HunterWhyte/WirelessLEDBracelet/media/case_render.png

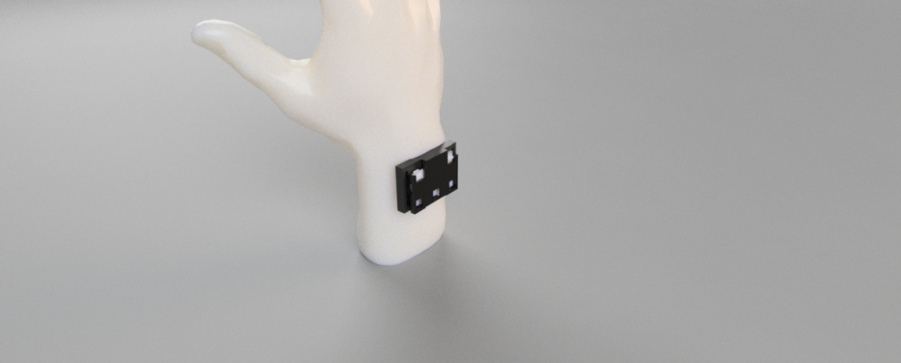
media/case_render.png
