HunterWhyte/WirelessLEDBracelet/bracelet_hardware/bracelet.sch

## EAGLE design bracelet_hardware/bracelet.sch (2023-08-14)

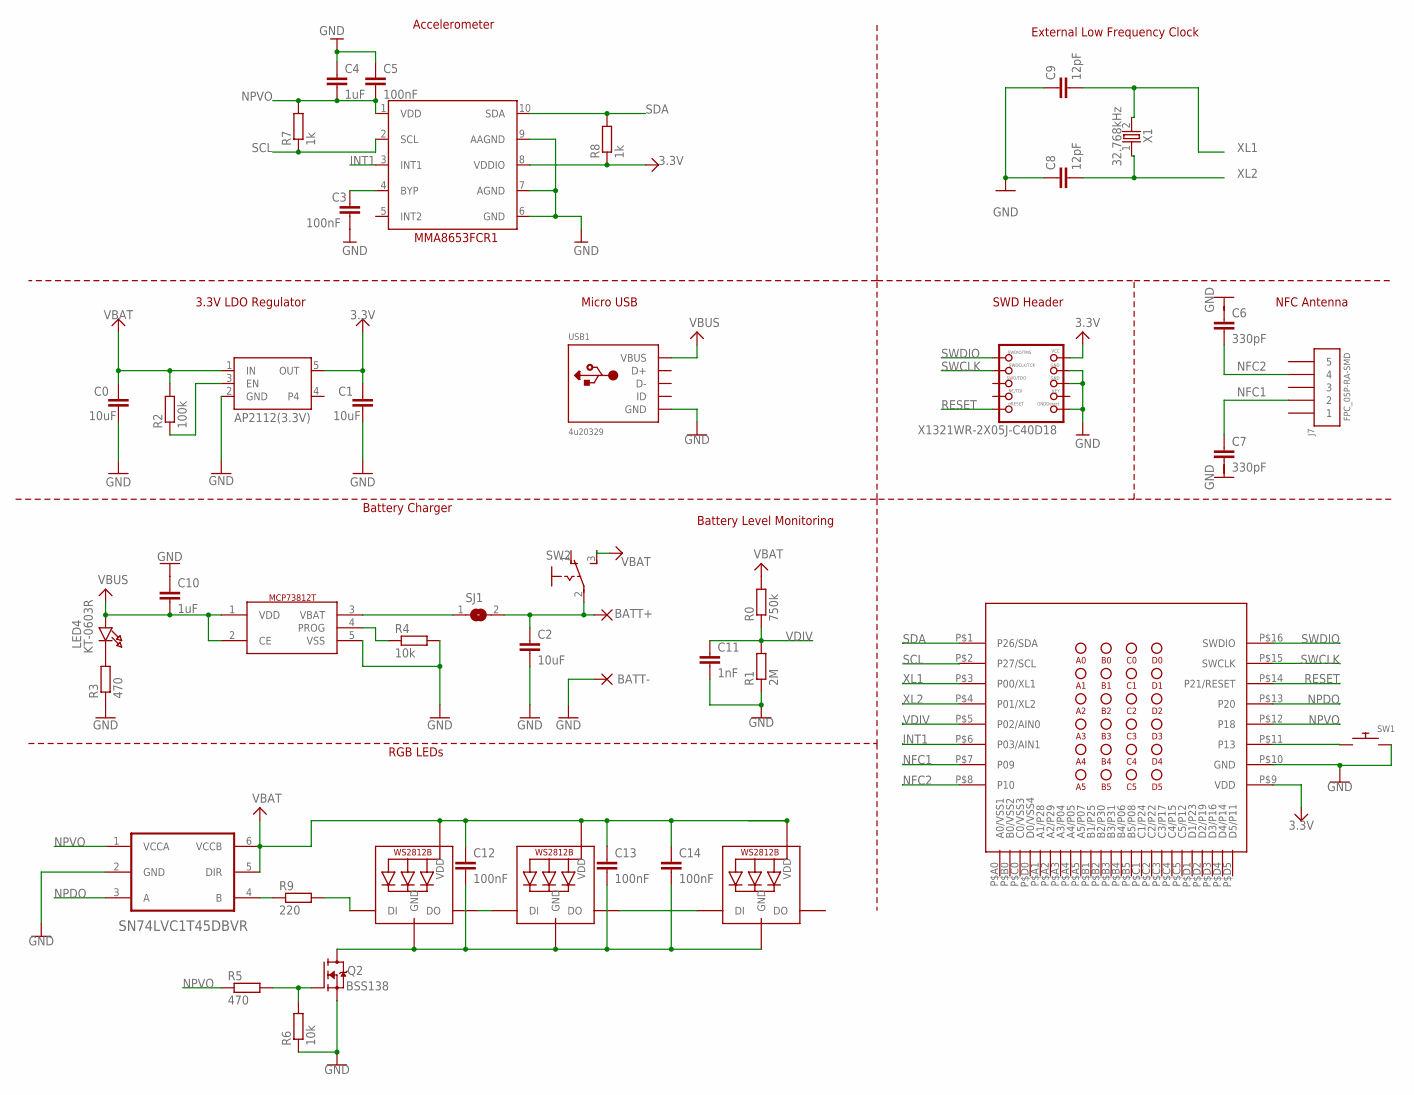
[picture p30: schematic bracelet.sch]

Parts:
BATT+: WIREPADSMD2,54-5,08; SMD2,54-5,08
BATT-: WIREPADSMD2,54-5,08; SMD2,54-5,08
C0, C1: 10uF; RESC0402_N
C2: 10uF; C0402
C3, C5, C12, C13, C14: 100nF; C0402
C4, C10: 1uF; C0402
C6, C7: 330pF; C0402
C8, C9: 12pF; C0402
C11: 1nF; C0402
J1: X1321WR-2X05J-C40D18; 2X05_1.27MM_BOX_POSTS
J7: FPC_05P-RA-SMD
LED1, LED2, LED3: WS2812B5050; WS2812B
LED4: LED0805_NOOUTLINE; CHIPLED_0805_NOOUTLINE
MMA8653FCR1: MMA8653FCR1
Q2: BSS138; SOT95P240X111-3N
R0: 750k; R0603
R1: 2M; R0603
R2: 100k; R0402
R3, R5: 470; R0402
R4, R6: 10k; R0402
R7, R8: 1k; R0402
R9: 220; R0402
SJ1: SJ
SW1: SWITCH_PUSHBUTTONSOFTTOUCHSMD_SJ; PUSHBUTTON_SMD_SJ
SW2: 255SB
U1: BT832L
U2: SN74LVC1T45DBVR; SOT95P280X145-6N
U3: AP2112(3.3V); SOT23-5
U$5: MCP73812T-420I/OT
USB1: 4u20329; 4UCONN_20329_V2
X1: 32.768kHz; XTAL_3215_N

Connections:
3.3V: C1.1, J1.1 (VCC), MMA8653FCR1.8 (VDDIO), R8.1, U1.P$9 (VDD), U3.5 (OUT)
GND: BATT-.1, C0.2, C1.2, C2.2, C3.2, C4.1, C5.1, C8.1, C9.1, C10.1, C11.2, J1.3 (GND), J1.5 (GND), J1.9 (GNDDETECT), MMA8653FCR1.6 (GND), MMA8653FCR1.7 (AGND), MMA8653FCR1.9 (AAGND), Q2.2 (S), R1.1, R3.1, R4.2, R6.1, SW1.P$2, U1.P$10 (GND), U2.2 (GND), U3.2 (GND), U$5.5 (VSS), USB1.BASE@1 (GND)
INT1: MMA8653FCR1.3 (INT1), U1.P$6 (P03/AIN1)
unnamed: LED1.2-DOUT (DO), LED2.4-DIN (DI)
unnamed: BATT+.1, C2.1, SJ1.2, SW2.2
unnamed: SW1.P$1, U1.P$11 (P13)
unnamed: R9.1, U2.4 (B)
unnamed: LED4.C, R3.2
unnamed: R2.1, U3.3 (EN)
unnamed: LED2.2-DOUT (DO), LED3.4-DIN (DI)
unnamed: SJ1.1, U$5.3 (VBAT)
unnamed: Q2.1 (G), R5.2, R6.2
unnamed: LED1.4-DIN (DI), R9.2
unnamed: R4.1, U$5.4 (PROG)
unnamed: C12.2, C13.2, C14.2, LED1.3-GND (GND), LED2.3-GND (GND), LED3.3-GND (GND), Q2.3 (D)
unnamed: C3.1, MMA8653FCR1.4 (BYP)
NFC1: C7.1, J7.2, U1.P$7 (P09)
NFC2: C6.2, J7.4, U1.P$8 (P10)
NPDO: U1.P$13 (P20), U2.3 (A)
NPVO: C4.2, C5.2, MMA8653FCR1.1 (VDD), R5.1, R7.2, U1.P$12 (P18), U2.1 (VCCA)
RESET: J1.10 (NRESET), U1.P$14 (P21/RESET)
SCL: MMA8653FCR1.2 (SCL), R7.1, U1.P$2 (P27/SCL)
SDA: MMA8653FCR1.10 (SDA), R8.2, U1.P$1 (P26/SDA)
SWCLK: J1.4 (SWDCLK), U1.P$15 (SWCLK)
SWDIO: J1.2 (SWDIO), U1.P$16 (SWDIO)
VBAT: C0.1, C12.1, C13.1, C14.1, LED1.1-VDD (VDD), LED2.1-VDD (VDD), LED3.1-VDD (VDD), R0.2, R2.2, SW2.3 (S), U2.5 (DIR), U2.6 (VCCB), U3.1 (IN)
VBUS: C10.2, LED4.A, U$5.1 (VDD), U$5.2 (CE), USB1.VBUS
VDIV: C11.1, R0.1, R1.2, U1.P$5 (P02/AIN0)
XL1: C9.2, U1.P$3 (P00/XL1), X1.2
XL2: C8.2, U1.P$4 (P01/XL2), X1.1

Notes on the sheet:
MMA8653FCR1
KT-0603R
RGB LEDs
Battery Charger
3.3V LDO Regulator
Battery Level Monitoring
NFC Antenna
External Low Frequency Clock
SWD Header
Micro USB
Accelerometer
